Xinyao-Wang/Alignment_System/Prototype 4/截图.png

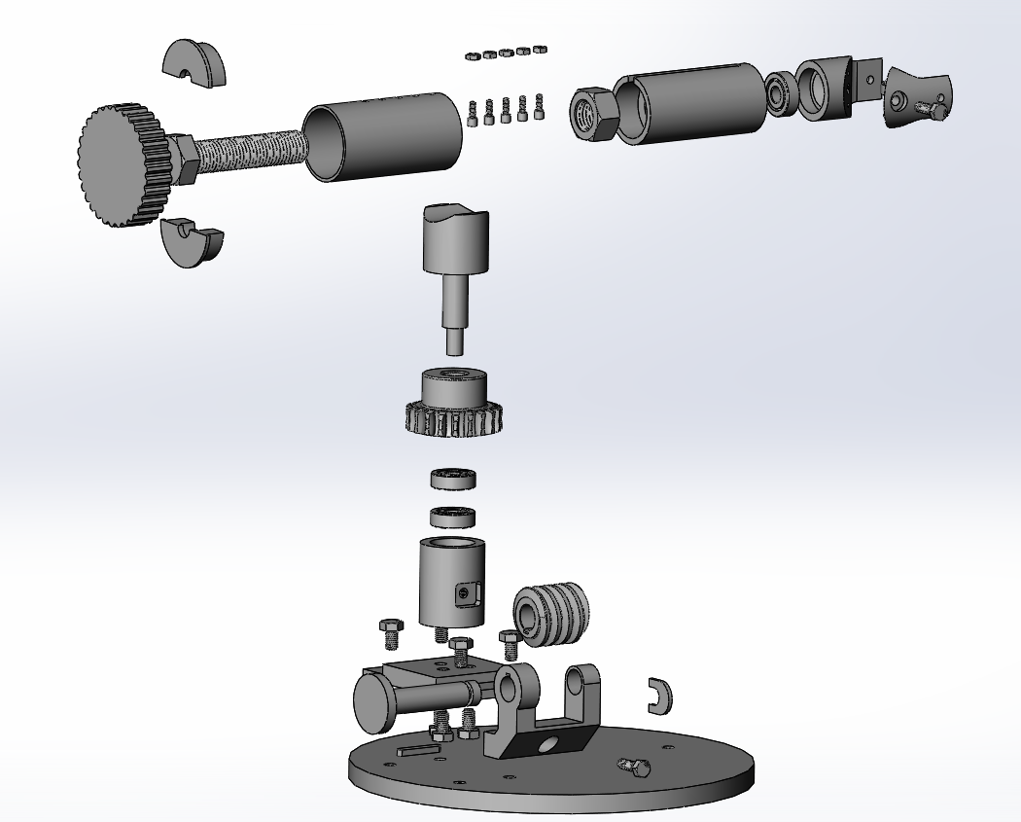
Prototype 4/截图.png
