Xinyao-Wang/Alignment_System/Prototype 4/Ball Bearing.SLDPRT

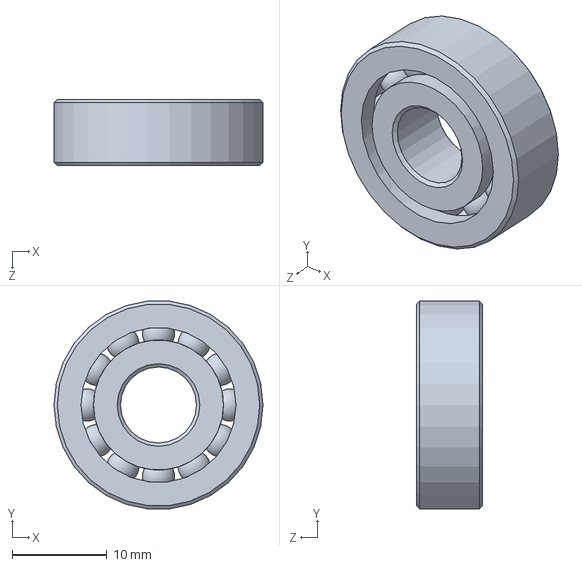
[picture p90: CAD file, 2020-11-08]
Prototype 4/Ball Bearing.SLDPRT
22.0 x 21.9 x 7.00 mm
