Xinyao-Wang/Alignment_System/Prototype 4/Bearing Inner Spacer.SLDPRT

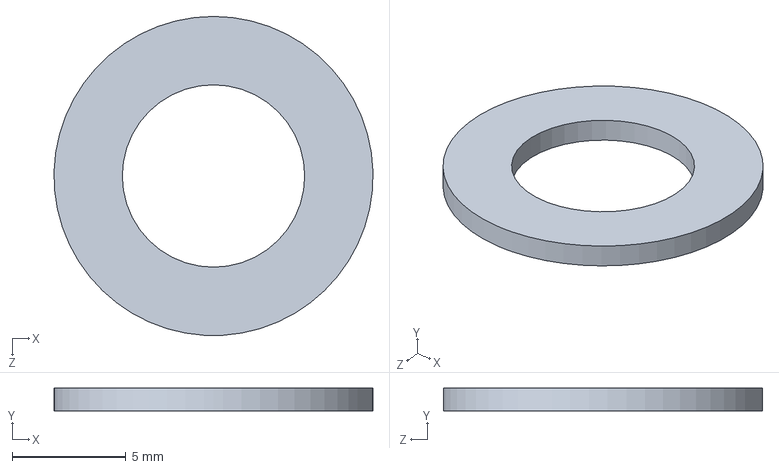
[picture p91: CAD file, 2020-11-08]
Prototype 4/Bearing Inner Spacer.SLDPRT
14.0 x 1.00 x 14.0 mm
