Xinyao-Wang/Alignment_System/Prototype 4/Worm.SLDPRT

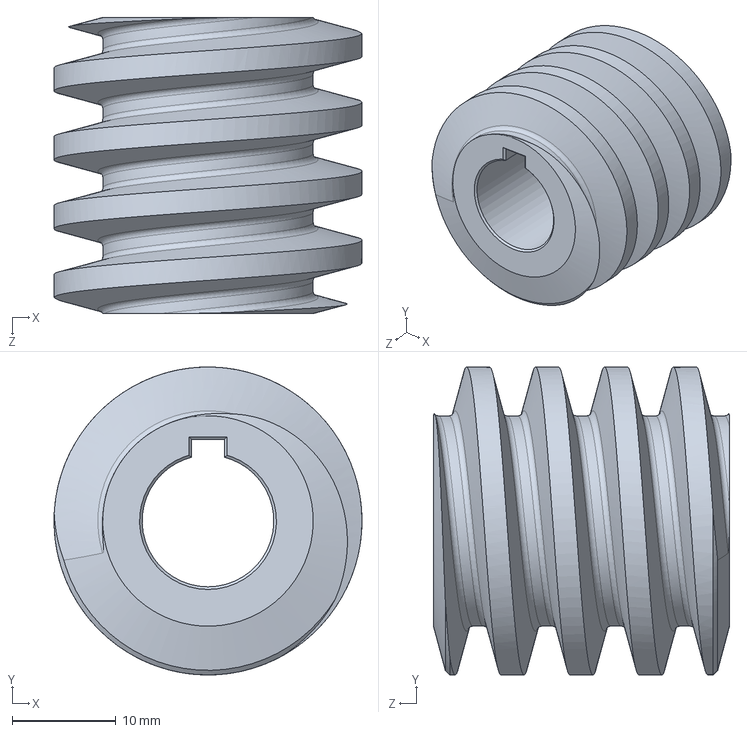
[picture p92: CAD file, 2020-11-08]
Prototype 4/Worm.SLDPRT
29.7 x 29.7 x 28.6 mm
