Xinyao-Wang/Alignment_System/Prototype 4/Base Adjustment Rod.SLDPRT

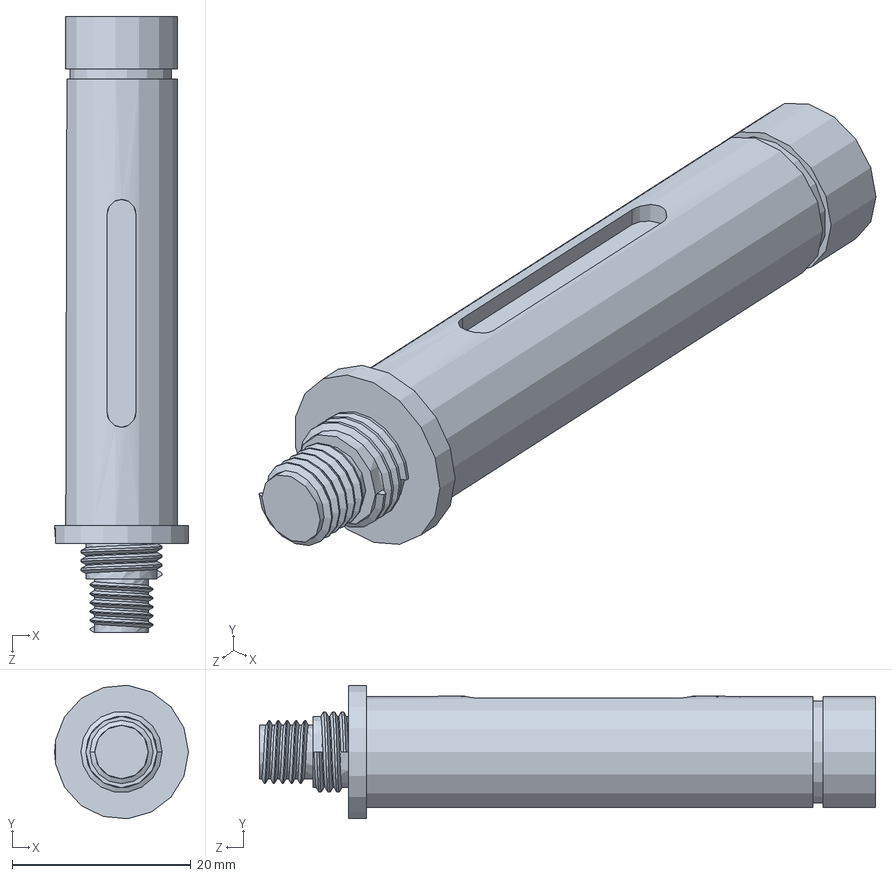
[picture p93: CAD file, 2020-11-08]
Prototype 4/Base Adjustment Rod.SLDPRT
15.0 x 14.9 x 69.0 mm
