Xinyao-Wang/Alignment_System/Prototype 4/Platform.SLDPRT

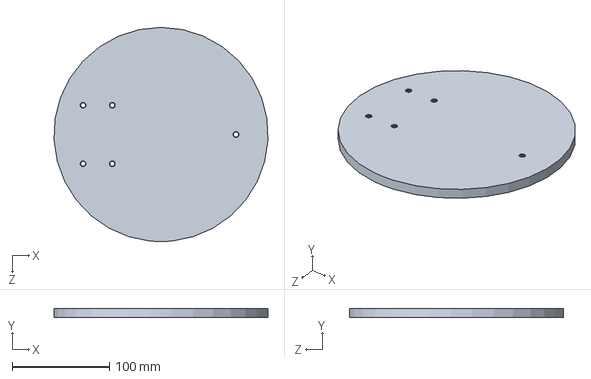
[picture p94: CAD file, 2020-11-08]
Prototype 4/Platform.SLDPRT
219.7 x 9.53 x 220.0 mm
