Xinyao-Wang/Alignment_System/Prototype 4/Base Rod.SLDPRT

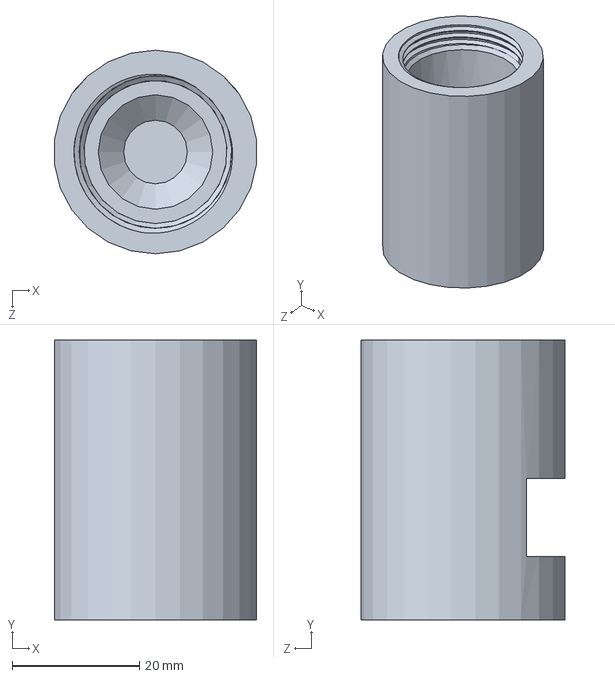
[picture p95: CAD file, 2020-11-08]
Prototype 4/Base Rod.SLDPRT
31.8 x 44.0 x 32.0 mm
