Xinyao-Wang/Alignment_System/Prototype 4/Rail Rod.SLDPRT

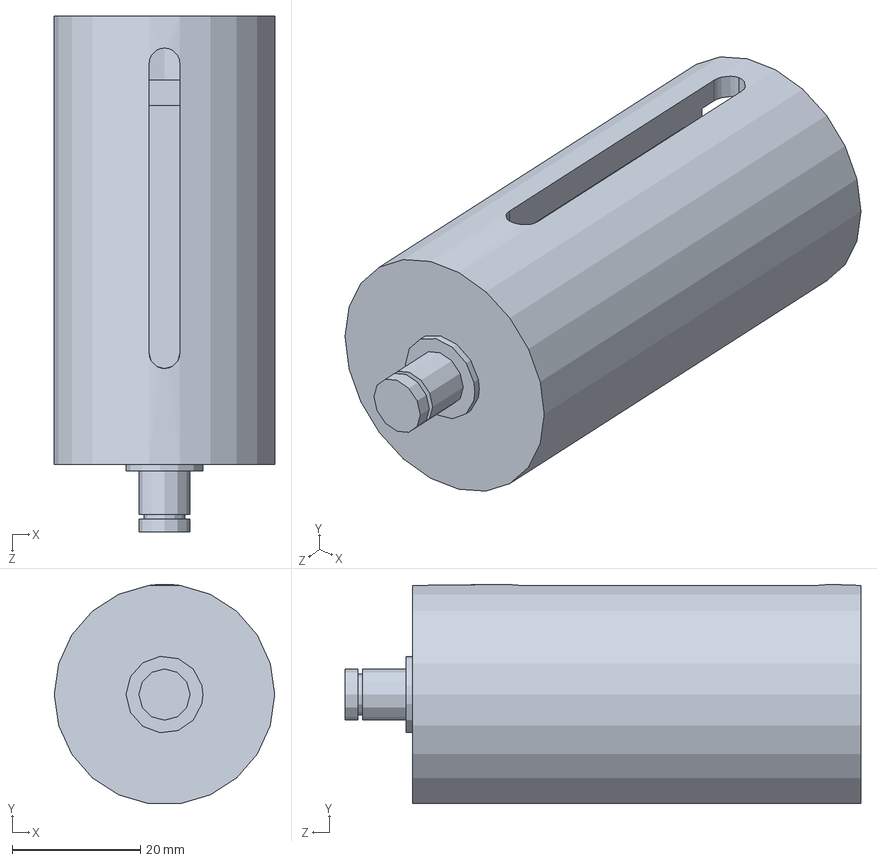
[picture p96: CAD file, 2020-11-08]
Prototype 4/Rail Rod.SLDPRT
34.4 x 34.2 x 80.5 mm
