Xinyao-Wang/Alignment_System/Prototype 4/Supporting Part for Sleeve 1.SLDPRT

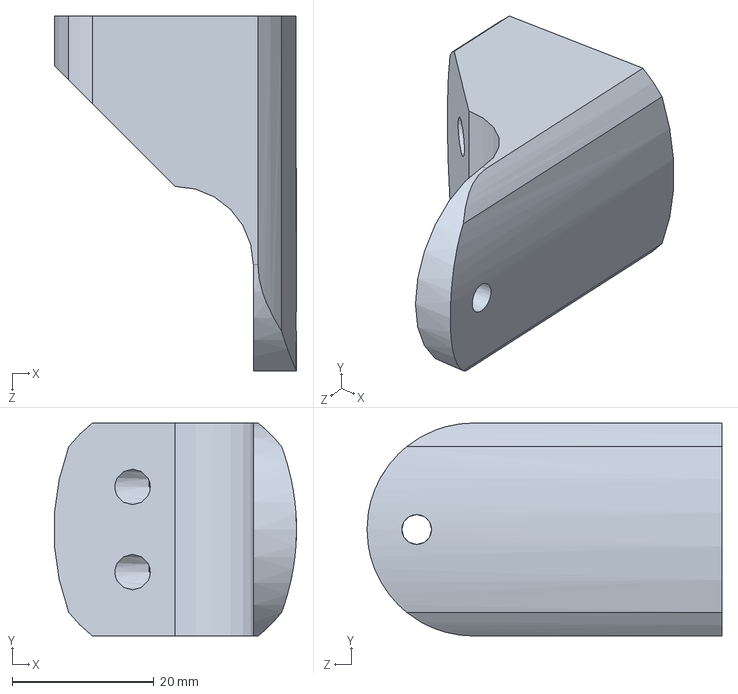
[picture p97: CAD file, 2020-11-08]
Prototype 4/Supporting Part for Sleeve 1.SLDPRT
34.1 x 30.0 x 50.0 mm
