Xinyao-Wang/Alignment_System/Prototype 4/Threaded Bearing Cover.SLDPRT

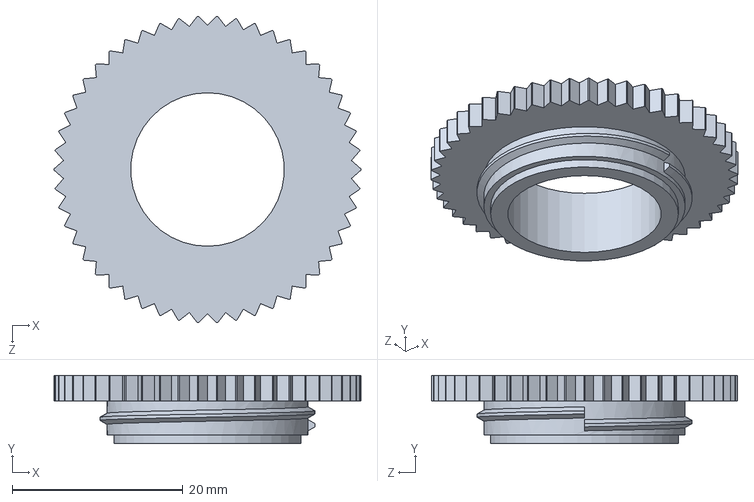
[picture p98: CAD file, 2020-11-08]
Prototype 4/Threaded Bearing Cover.SLDPRT
36.0 x 8.00 x 35.9 mm
