Xinyao-Wang/Alignment_System/Prototype 4/Supporting Rod for Shell.SLDPRT

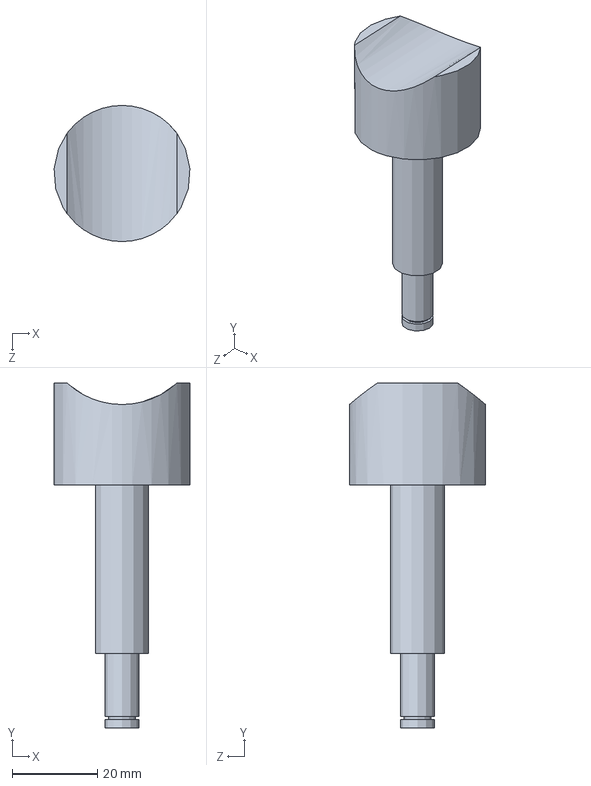
[picture p99: CAD file, 2020-11-08]
Prototype 4/Supporting Rod for Shell.SLDPRT
31.9 x 81.1 x 32.0 mm
