Xinyao-Wang/Alignment_System/Prototype 4/Laser Pen.SLDPRT

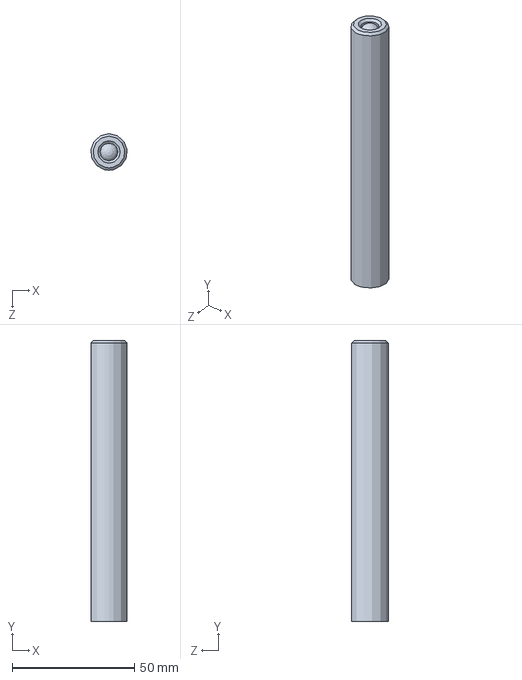
[picture p100: CAD file, 2020-11-08]
Prototype 4/Laser Pen.SLDPRT
14.9 x 115.0 x 15.0 mm
