Xinyao-Wang/Alignment_System/Prototype 4/Supporting Part for Worm.SLDPRT

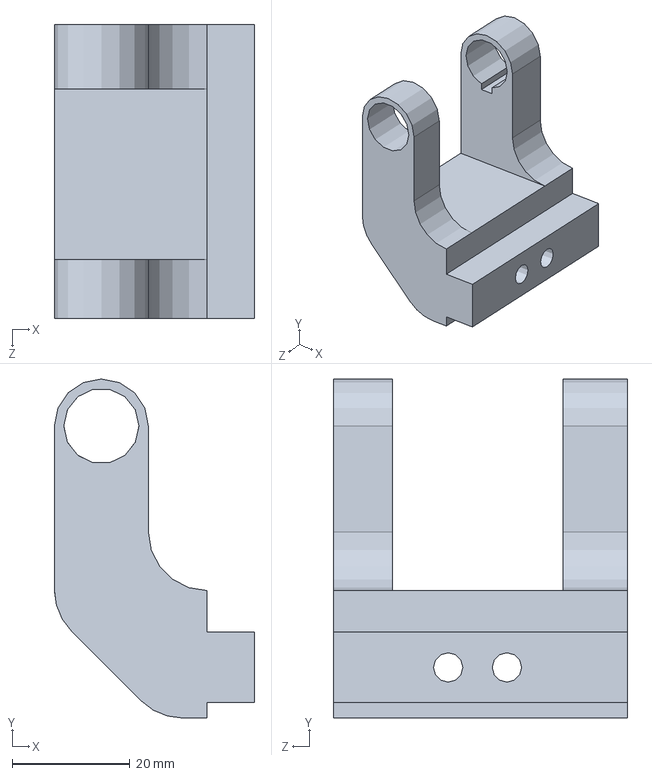
[picture p101: CAD file, 2020-11-08]
Prototype 4/Supporting Part for Worm.SLDPRT
34.1 x 57.7 x 50.0 mm
