Xinyao-Wang/Alignment_System/Prototype 4/Sleeve.SLDPRT

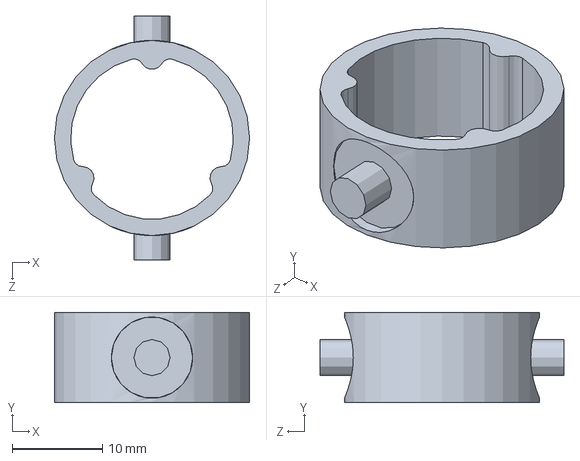
[picture p102: CAD file, 2020-11-08]
Prototype 4/Sleeve.SLDPRT
21.6 x 10.0 x 27.0 mm
