Xinyao-Wang/Alignment_System/Prototype 4/Spring.SLDPRT

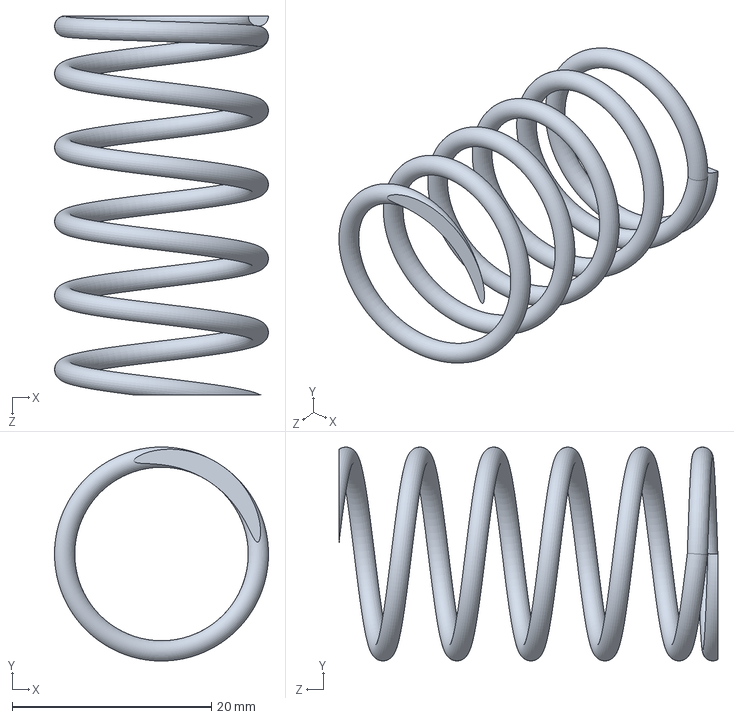
[picture p103: CAD file, 2020-11-08]
Prototype 4/Spring.SLDPRT
21.5 x 21.5 x 38.0 mm
